doleynikov/mk61avr/arduino_BASIC/arduino_BASIC.ino

// Адаптировано!
// Работает! 1.6.5
// сделать ввод с сериального порта! в файле host.cpp

#include "Arduino.h"
#include <EEPROM.h>

#include "basic.h"
#include "host.h"

// buzzer pin, 0 = disabled/not present
#define BUZZER_PIN    9

// BASIC
unsigned char mem[MEMORY_SIZE];
#define TOKEN_BUF_SIZE    64
unsigned char tokenBuf[TOKEN_BUF_SIZE];

const char welcomeStr[] PROGMEM = "Arduino BASIC";
char autorun = 0;

void setup() {

    Serial.begin(9600);   // opens serial port, sets data rate to 9600 bps

    reset();
    host_init(BUZZER_PIN);
    host_cls();
    host_outputProgMemString(welcomeStr);
    // show memory size
    host_outputFreeMem(sysVARSTART - sysPROGEND);
    
    if (EEPROM.read(0) == MAGIC_AUTORUN_NUMBER)
        autorun = 1;
    else
        host_startupTone();
}

void loop() {
    int ret = ERROR_NONE;

    if (!autorun) {
        // get a line from the user
        char *input = host_readLine();
        // special editor commands
        if (input[0] == '?' && input[1] == 0) {
            host_outputFreeMem(sysVARSTART - sysPROGEND);
            return;
        }
        // otherwise tokenize
        ret = tokenize((unsigned char*)input, tokenBuf, TOKEN_BUF_SIZE);
    }
    else {
        host_loadProgram();
        tokenBuf[0] = TOKEN_RUN;
        tokenBuf[1] = 0;
        autorun = 0;
    }
    // execute the token buffer
    if (ret == ERROR_NONE) {
        host_newLine();
//        host_outputProgMemString((char *)pgm_read_word(&(errorTable[ret])));
        ret = processInput(tokenBuf);
    }
    if (ret != ERROR_NONE) {
        host_newLine();
        if (lineNumber !=0) {
            host_outputInt(lineNumber);
            host_outputChar('-');
        }
        host_outputProgMemString((char *)pgm_read_word(&(errorTable[ret])));
        host_newLine();
    }
}
