doleynikov/mk61avr/keyboard.c

// ***********************************************************
// Project: Эмулятор программируемого калькулятора МК-61 на AVR:
// https://github.com/doleynikov/mk61avr
//
// Copyright (с) 2017 Алексей Сугоняев, Виталий Самуров, Дмитрий Олейников
//
// Module name: keyboard.c
//
// Module description:
//
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
// ***********************************************************
//
#include "config.h"
#include <avr/io.h>
#include <avr/interrupt.h>
#include <avr/pgmspace.h>
#include "micro_os.h"
#include "keyboard.h"
#include "time.h"
#include "mk61types.h"

// Глобальные переменные
sTimeTask *sDTRIM;
sTimeTask *sSCANP;
sTimeTask *sSCANR;

void TASK_DTRIM(void);
void TASK_SCAN_PRESS(void);
void TASK_SCAN_RELEASE(void);

unsigned char RowScan;
uScanCode ScanCode;


/*************************************************************************
Name: Keyboard_Init

Input:    none

Returns:  none
*************************************************************************/
void Keyboard_Init(void)
{
    RowScan  = 0x08;
    ScanCode.val = 0x00;

    // Загрузка планировщика задачами обслуживания клавиатуры
    sDTRIM = TIME_AppendTask(TASK_DTRIM, TIME_DRIBLING_WAIT, TIME_TASK_SKIP|TIME_TASK_UNITARY);
    sSCANR = TIME_AppendTask(TASK_SCAN_RELEASE, TIME_10ms, TIME_TASK_SKIP|TIME_TASK_UNITARY);
    sSCANP = TIME_AppendTask(TASK_SCAN_PRESS, TIME_10ms, TIME_TASK_SKIP|TIME_TASK_UNITARY);
    Keyboard_Scan();
}


/*************************************************************************
Name: TASK_DTRIM

Input:    none

Returns:  none

    ######## ѕЋјЌ»–”≈“—я Ў≈ƒ”Ћ≈–ќћ ########
    Однократнозапускаемая задача подавления дребезга контактов - и проверка после
    подавления нажатия.
    Время подавления Thold =  0.4 сек
*************************************************************************/
void TASK_DTRIM(void)
{
    register unsigned char KEY;
    register unsigned char tmp=9;

    // Определяем скан-код
    KEY = ~KEY_P0;
    asm volatile
    (
        "sec"                           "\n\t"
        "loop%=:" "dec %[cnt]"          "\n\t"
        "rol %[key]"                    "\n\t"
        "brcc loop%="                   "\n\t"
        : [cnt] "+r" (tmp), [key] "+r" (KEY)
        :
    );

    KEY = (~KEY_P1)&(MASK_KEY_P1);
    if(KEY)
    {
        KEY += 8;
    }

    if((KEY += tmp))
    {
        // после таймаута по дребезгу, с клавиатуры считан код - поднимаем
        // задачу ожидания освобождения клавиатуры
        TIME_UpTask(sSCANR);
        ScanCode.val = KEY|RowScan;
    }
    else
    {
        // после подавления дребезга клавиатура не активна (ложное срабатывание)
        // ожидаем нажатия
        TIME_UpTask(sSCANP);
    }
}


/*************************************************************************
Name: SetScanLine

Input:    none

Returns:  none
*************************************************************************/
void SetScanLine(void)
{
}


/*************************************************************************
Name: TASK_SCAN_PRESS

Input:    none

Returns:  none

    ######## ѕЋјЌ»–”≈“—я Ў≈ƒ”Ћ≈–ќћ ########
    Однократнозапускаемая задача сканирования строк клавиатурной матрицы и
    проверки на нажатие
    Tscan =  0.01 сек
*************************************************************************/
void TASK_SCAN_PRESS(void)
{
    // Считываем состояние линий портов клавиатурых строки
    register unsigned char KEYS = KEY_P0 - (KEY_P1|(~MASK_KEY_P1));
    if(KEYS)
    {
        TIME_UpTask(sDTRIM); //  Клавиатура активна - поднимаем задачу подавления дребезга
    }
    else
    {
        //  Клавиатура не активна, переходим к сканированию следующей линии
        KEYS = RowScan << 1;
        if(KEYS == 0)
        {
            KEYS = 0x10;  // циклическая смена, переход на младшую линию сканирования
        }

        RowScan = KEYS;
        asm volatile
        (
            "push r28"                  "\n\t"
            "in   r28, %[scanport]"     "\n\t"
            "ori  r28, ~%[scanmask]"    "\n\t"
            "eor  r28, %[rowscan]"      "\n\t"  // копируем разряды скан-кода с доп. инверсией
            "out %[scanport], r28"      "\n\t"  // плюнем в порт сканирования поддтяжки к VCC
            "in   r28, %[scanddr]"      "\n\t"  // синтезируем порт направления
            "andi r28, %[scanmask]"     "\n\t"
            "or   r28, %[rowscan]"      "\n\t"  // копируем разряды скан-кода
            "out %[scanddr], r28"       "\n\t"
            "pop r28"
            :
            : [scanddr]  "I" (_SFR_IO_ADDR(SCANDDR)),
            [scanport] "I" (_SFR_IO_ADDR(SCANPORT)),
            [scanmask] "M" (MASK_SCANLINE),
            [rowscan]  "r" (RowScan)
        );

        TIME_UpTask(sSCANP);
    }
}


/*************************************************************************
Name: TASK_SCAN_RELEASE

Input:    none

Returns:  none

    ######## ѕЋјЌ»–”≈“—я Ў≈ƒ”Ћ≈–ќћ ########
    Однократнозапускаемая задача сканирования строк клавиатурной матрицы и проверки
    на нажатие
    Tscan =  0.01 сек
*************************************************************************/
void TASK_SCAN_RELEASE(void)
{
    // —читываем состояние портов клавиатуры колонки и строки
    register unsigned char KEYS = KEY_P0 - (KEY_P1|(~MASK_KEY_P1));
    if(!KEYS)
    {
        OS.FLAGS.KEYBRD = 1; // Клавиатура неактивна - сообщим ќ— о том что клавиатура выдала код
    }
    else
    {
        TIME_UpTask(sSCANR);
    }
}



/*************************************************************************
Name: Keyboard_Scan

Input:    none

Returns:  none

    Код клавиши обработан ќ—, разрешаем сканирование далее
*************************************************************************/
void Keyboard_Scan(void)
{
    OS.FLAGS.KEYBRD = 0;
    TIME_UpTask(sSCANP);
}
