doleynikov/mk61avr/KB_test/Simple_Test/Simple_Test.ino

/*  PS2Keyboard library example
  
  PS2Keyboard now requries both pins specified for begin()

  keyboard.begin(data_pin, irq_pin);
  
  Valid irq pins:
     Arduino Uno:  2, 3
     Arduino Due:  All pins, except 13 (LED)
     Arduino Mega: 2, 3, 18, 19, 20, 21
     Teensy 2.0:   All pins, except 13 (LED)
     Teensy 2.0:   5, 6, 7, 8
     Teensy 1.0:   0, 1, 2, 3, 4, 6, 7, 16
     Teensy++ 2.0: 0, 1, 2, 3, 18, 19, 36, 37
     Teensy++ 1.0: 0, 1, 2, 3, 18, 19, 36, 37
     Sanguino:     2, 10, 11
  
  for more information you can read the original wiki in arduino.cc
  at http://www.arduino.cc/playground/Main/PS2Keyboard
  or http://www.pjrc.com/teensy/td_libs_PS2Keyboard.html
  
  Like the Original library and example this is under LGPL license.
  
  Modified by Cuninganreset@gmail.com on 2010-03-22
  Modified by Paul Stoffregen <paul@pjrc.com> June 2010
*/
   
#include "matrixKB.h"


matrixKB keyboard;

void setup() {
  delay(1000);
  keyboard.begin();
  Serial.begin(9600);
  Serial.println("Keyboard Test:");
}

void loop() {
  if (keyboard.available()) {
    
    // read the next key
    char c = keyboard.read();
      
      // otherwise, just print all normal characters
      Serial.print(c);
    }
  }
